Forge-Media/ai03-macropad-pcb/references/reference_images/1row1col_macropad_direct_to_GPIOs_002.png

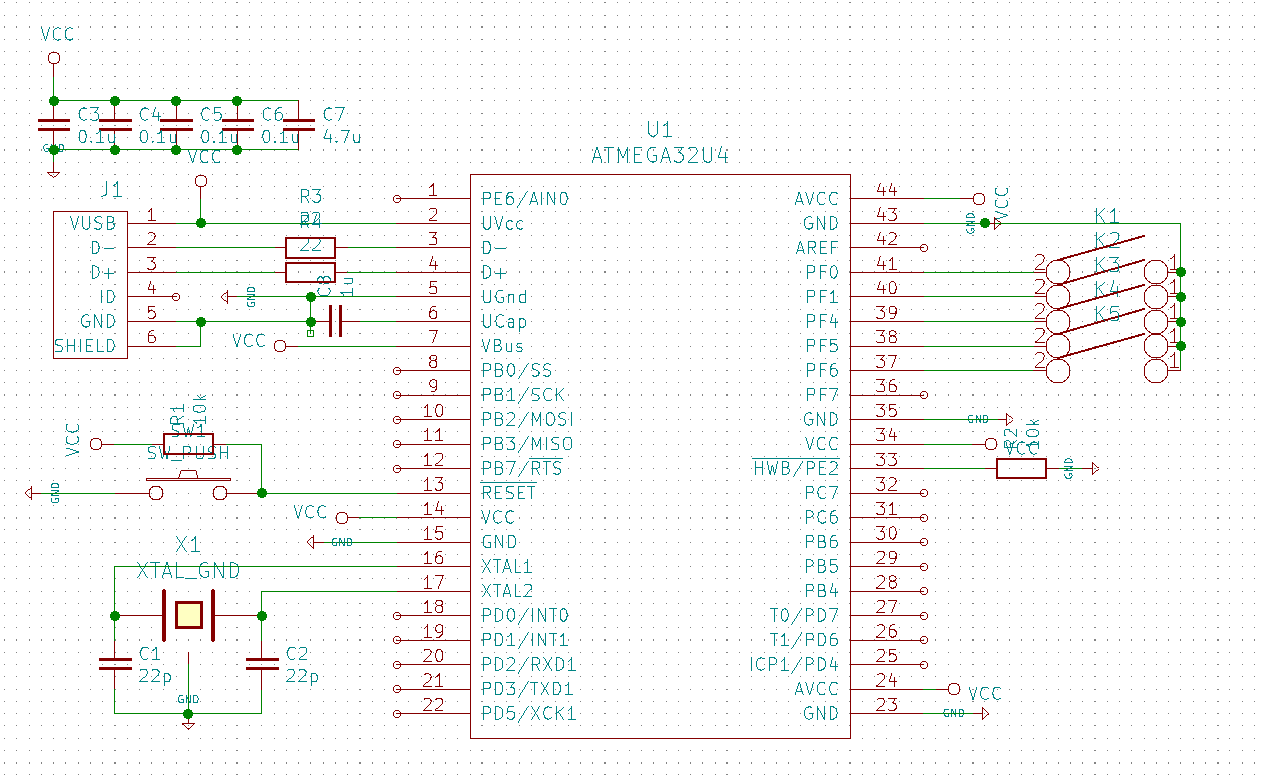
references/reference_images/1row1col_macropad_direct_to_GPIOs_002.png
