Forge-Media/ai03-macropad-pcb/references/reference_images/aio03_voyager4.png

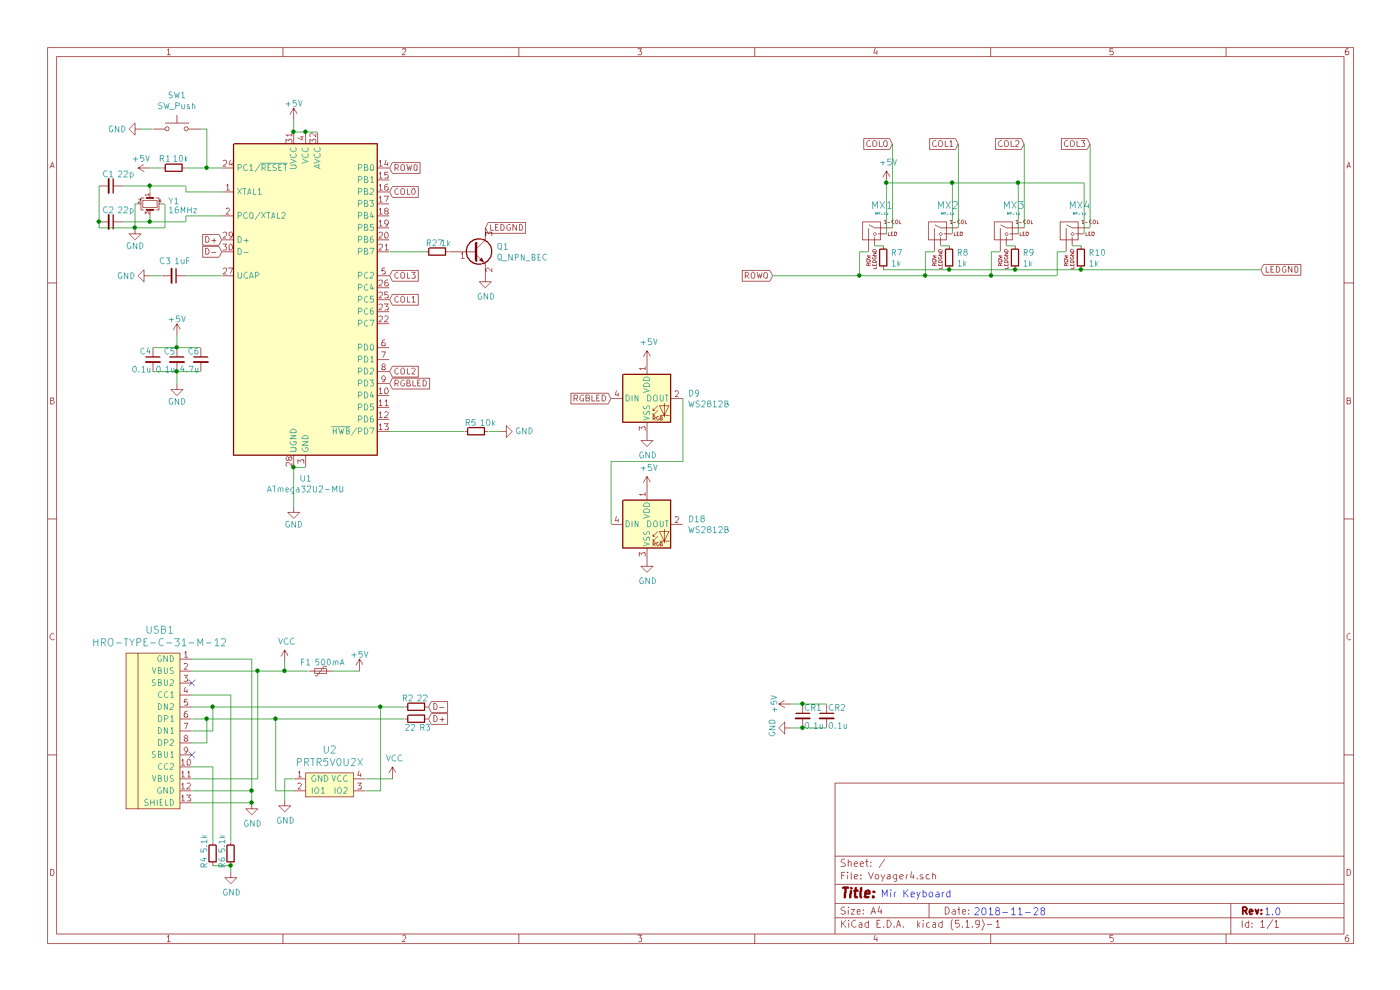
references/reference_images/aio03_voyager4.png
