Forge-Media/ai03-macropad-pcb/references/reference_images/aio03_voyager20.png

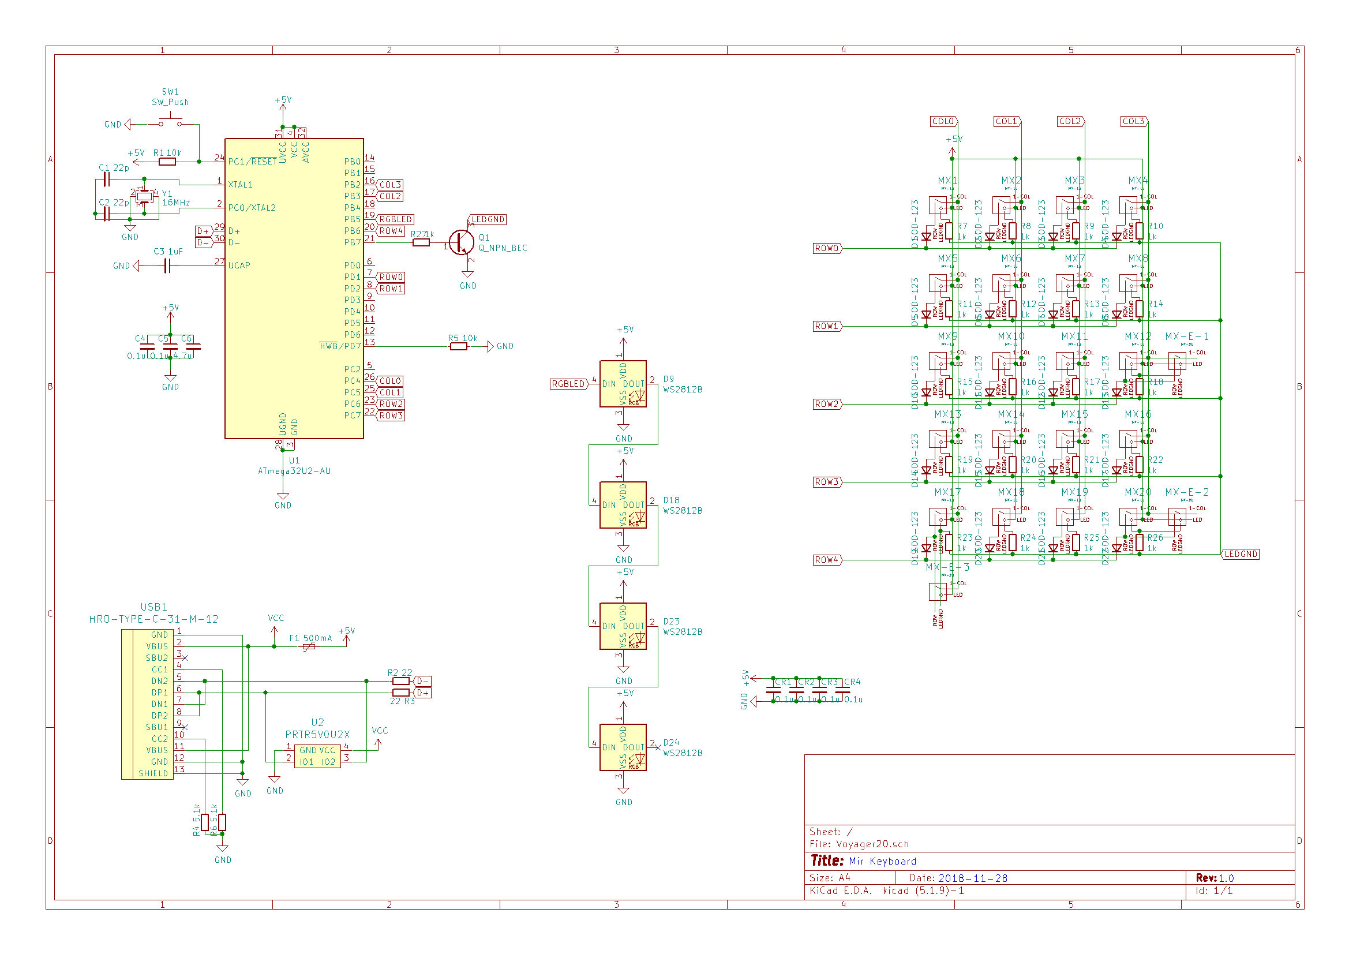
references/reference_images/aio03_voyager20.png
