Forge-Media/ai03-macropad-pcb/references/reference_images/easyeda_kTNAPJGku1.png

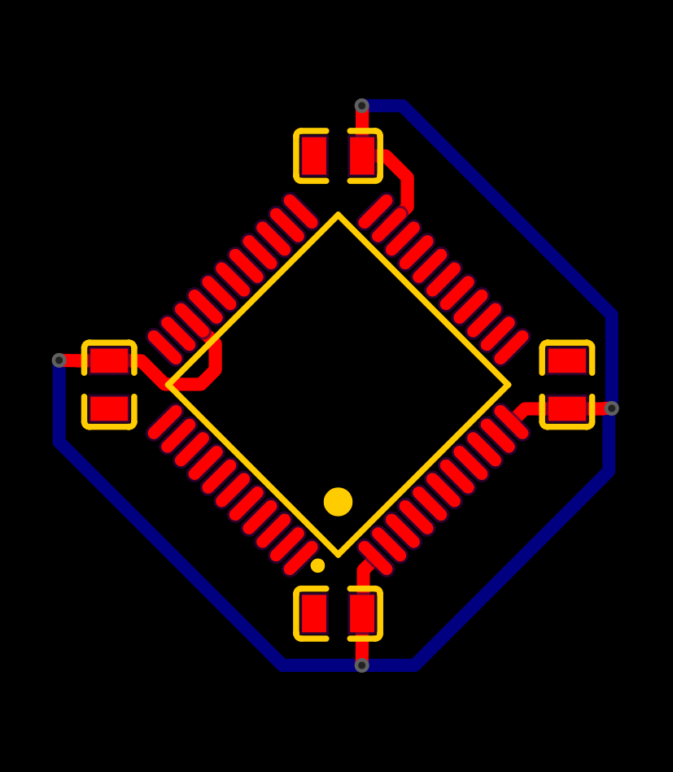
references/reference_images/easyeda_kTNAPJGku1.png
