Forge-Media/ai03-macropad-pcb/references/reference_images/rgb_led_reverse_mount_footprint.png

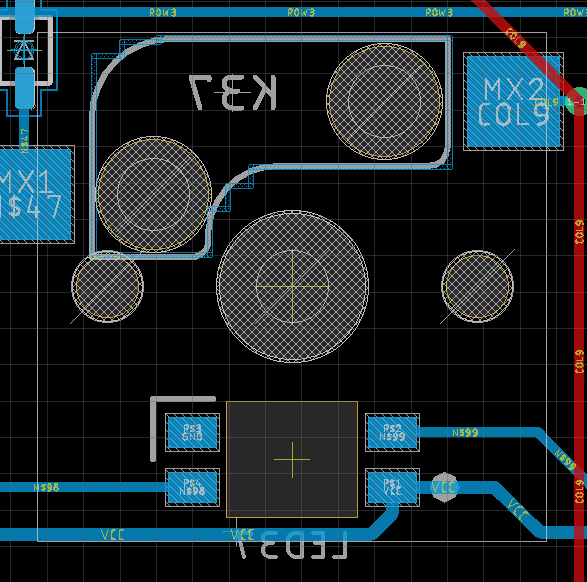
references/reference_images/rgb_led_reverse_mount_footprint.png
