Forge-Media/ai03-macropad-pcb/references/reference_images/unknown-2.png

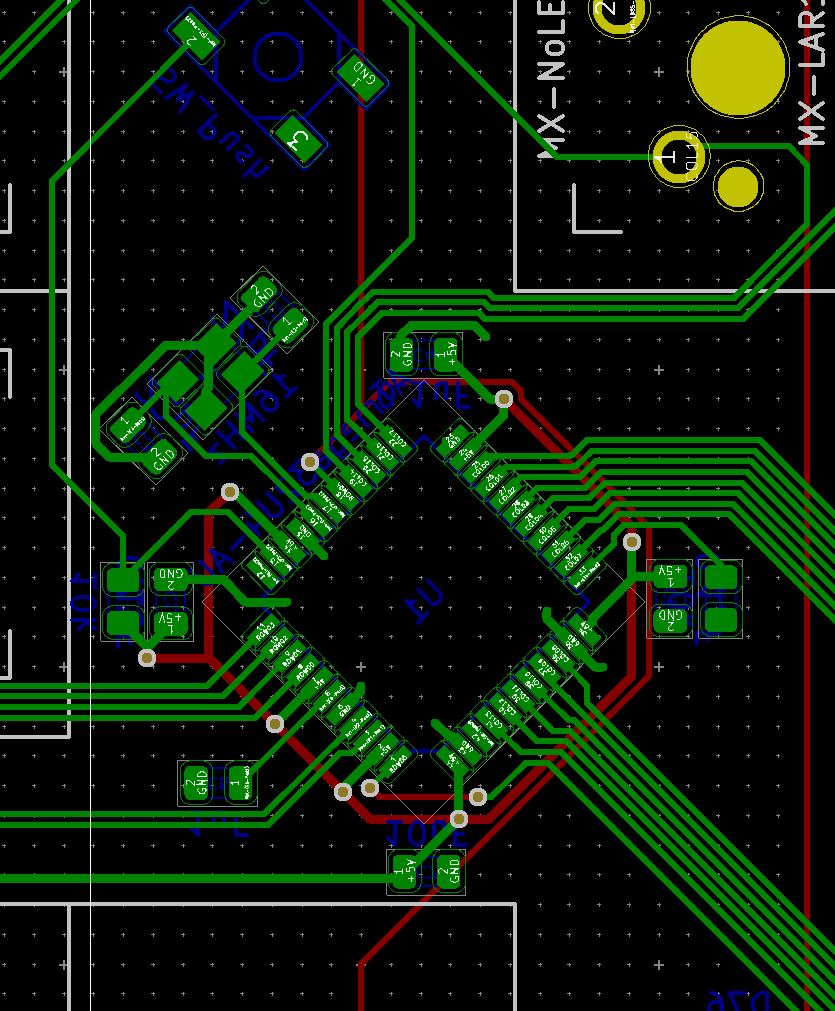
references/reference_images/unknown-2.png
