Forge-Media/ai03-macropad-pcb/references/reference_images/USB_Type-C_simplified_schematic_ESD.png

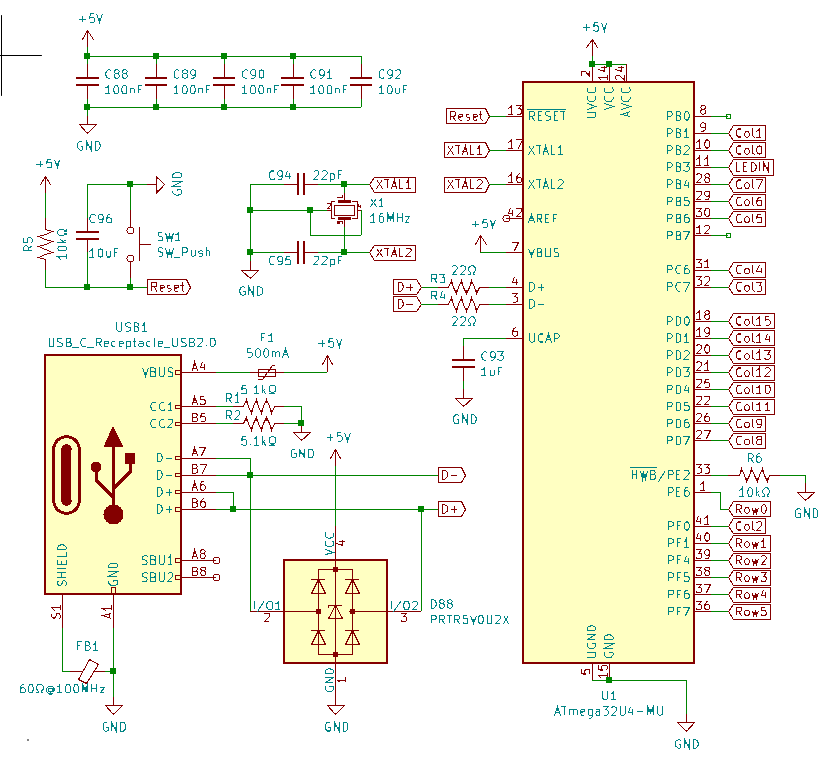
references/reference_images/USB_Type-C_simplified_schematic_ESD.png
