Forge-Media/ai03-macropad-pcb/references/specifications/usb_c_emi_ferrite_bead.png

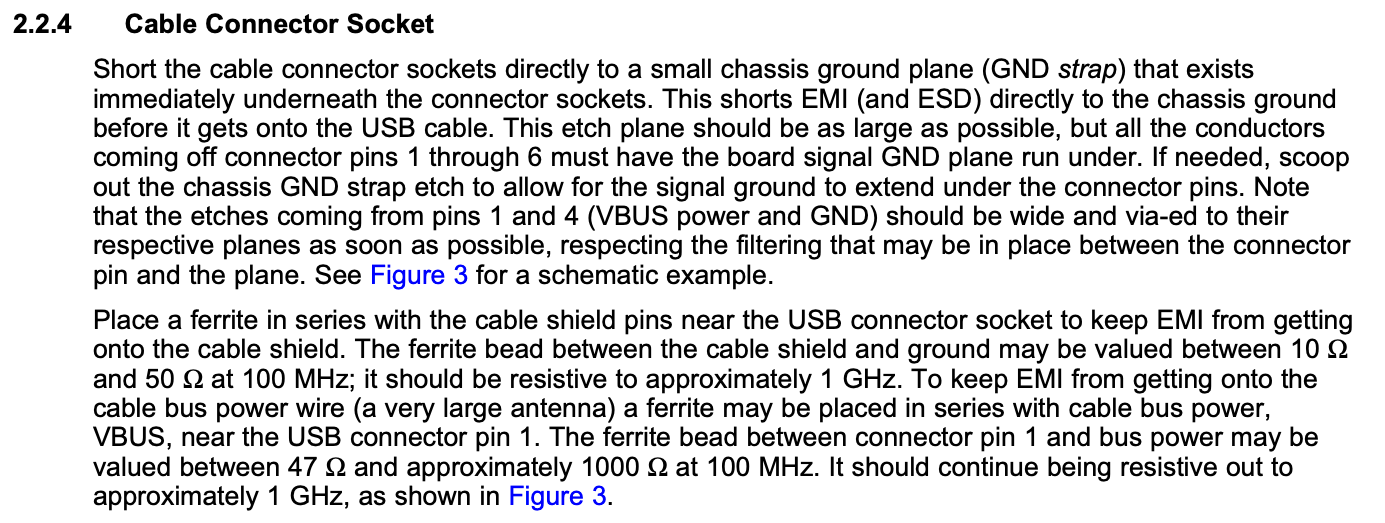
references/specifications/usb_c_emi_ferrite_bead.png
