Forge-Media/ai03-macropad-pcb/references/reference_images/basic_macropad_usb_mini_tested_working.png

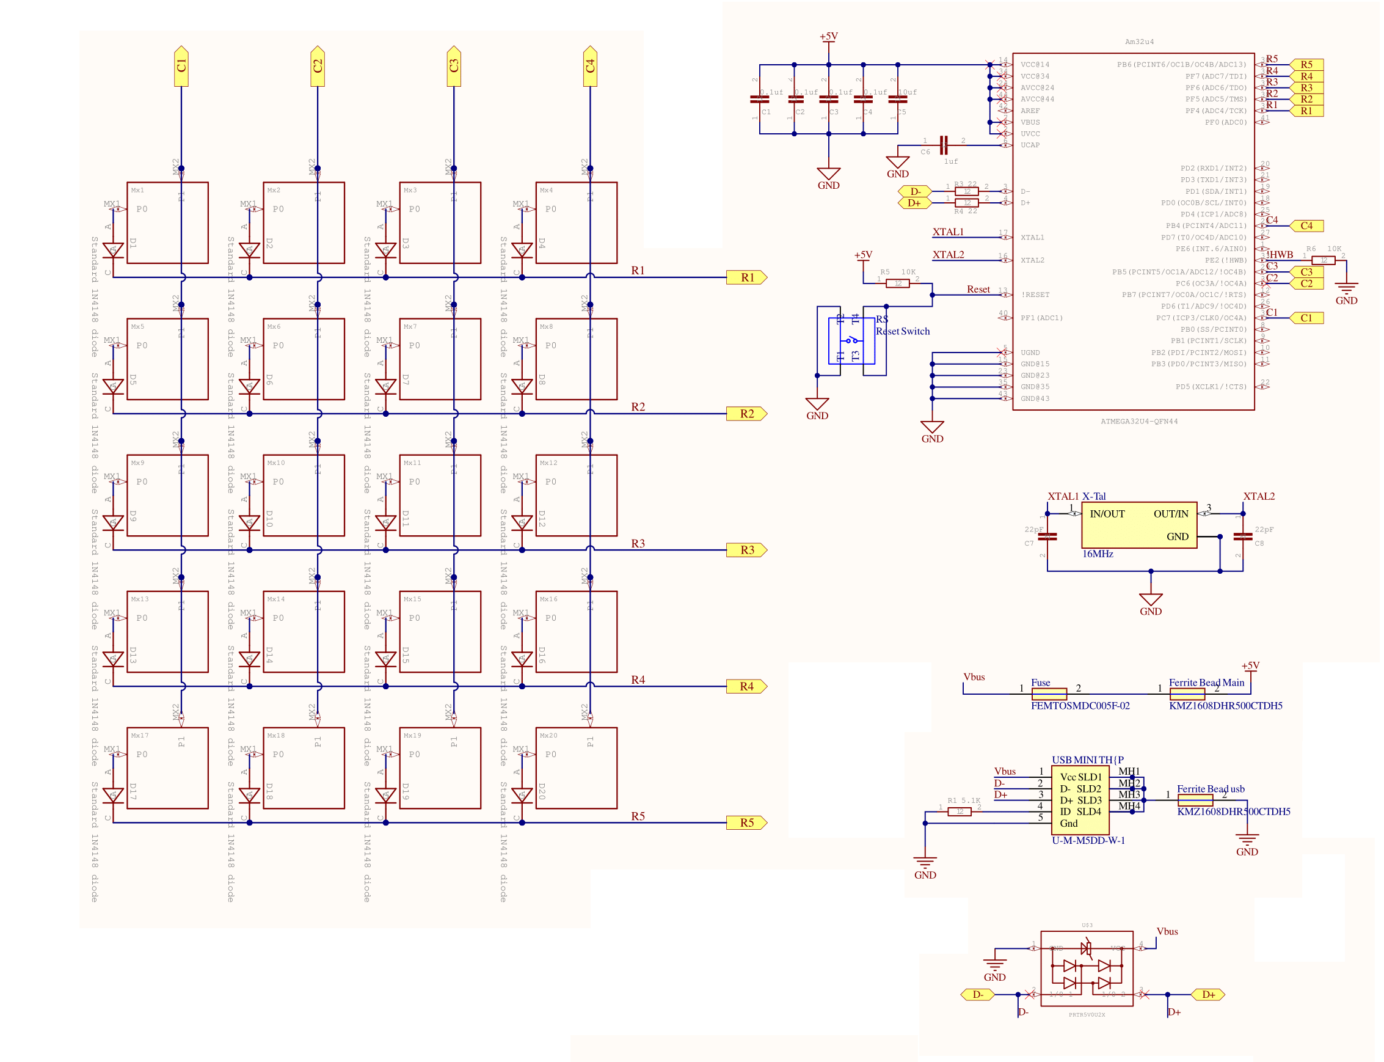
references/reference_images/basic_macropad_usb_mini_tested_working.png
